ItsMajestiX/gol-card/docs/img/img_7776.jpeg

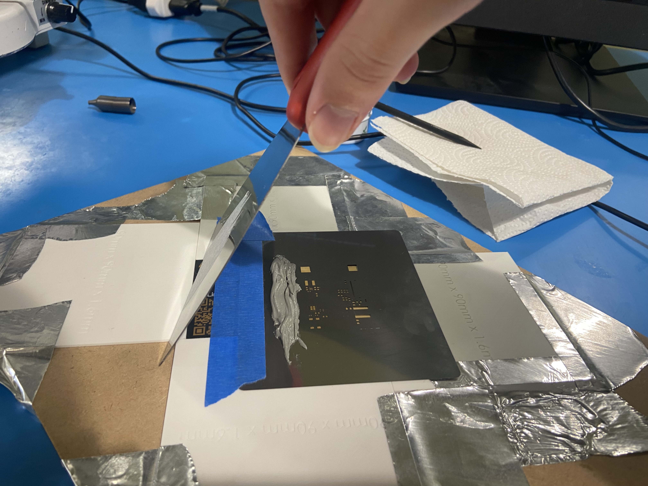
docs/img/img_7776.jpeg
