ItsMajestiX/gol-card/docs/img/img_7778.jpeg

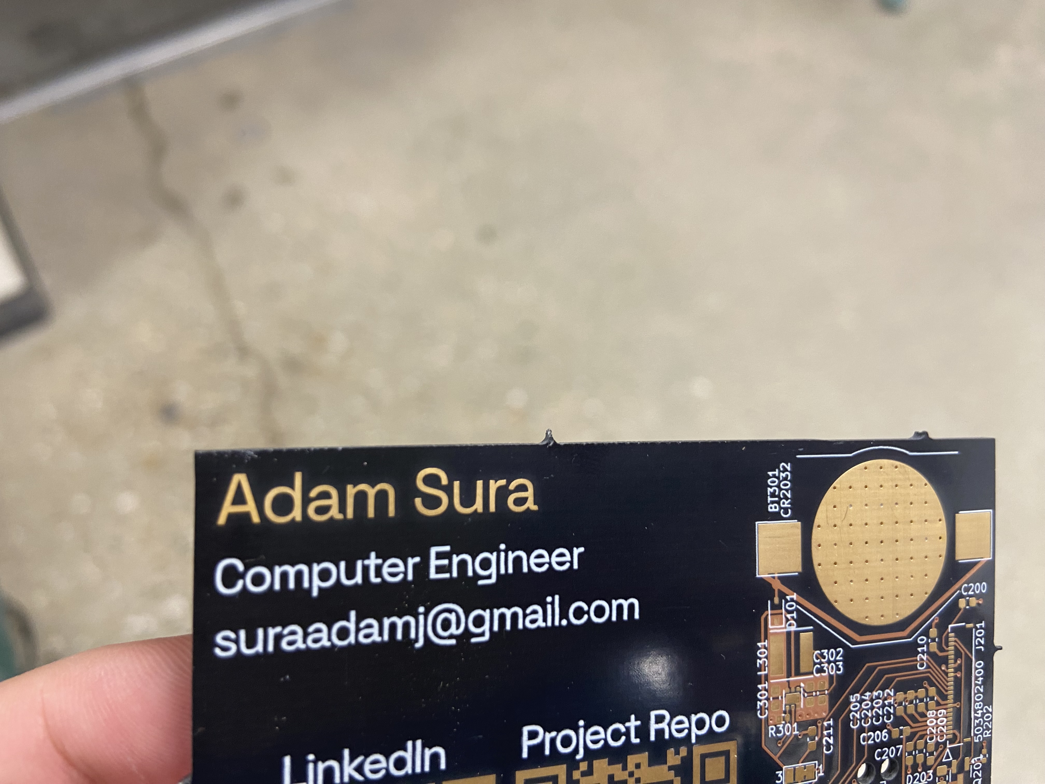
docs/img/img_7778.jpeg
