ItsMajestiX/gol-card/docs/img/img_7781.jpeg

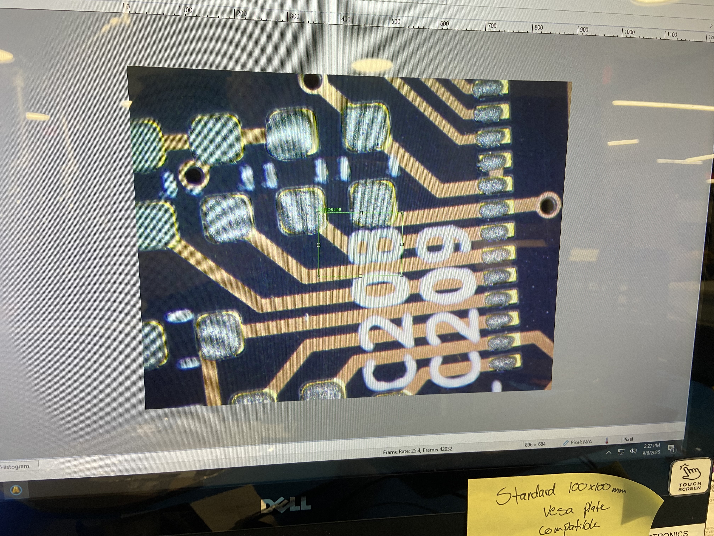
docs/img/img_7781.jpeg
