ItsMajestiX/gol-card/docs/img/img_7807.jpeg

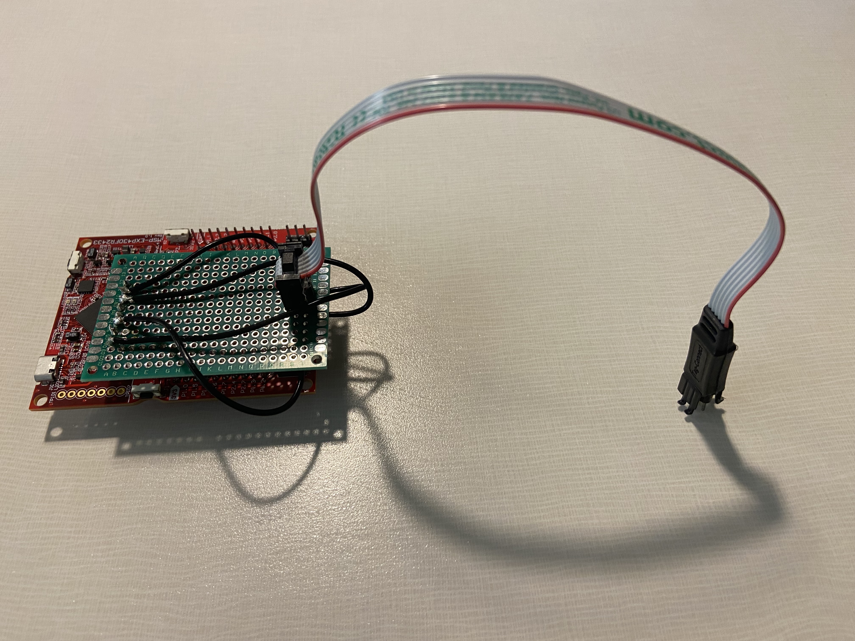
docs/img/img_7807.jpeg
