ItsMajestiX/gol-card/gol_card_pcb/graphic_silk.png

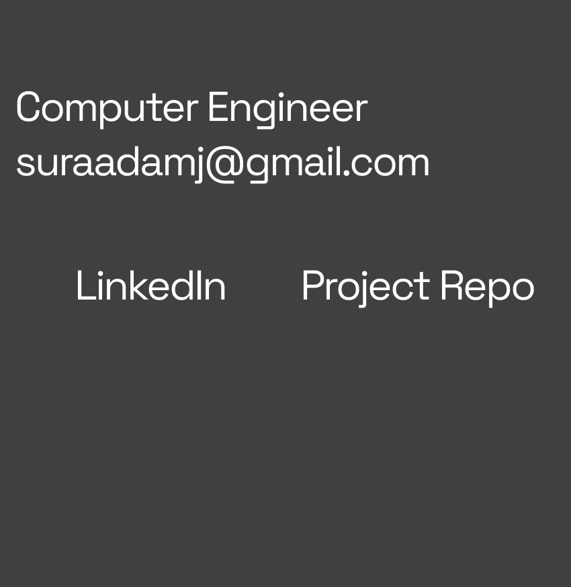
gol_card_pcb/graphic_silk.png
